adsehgal/SlugCharge/3D Housing Model/3D_Internal.jpg

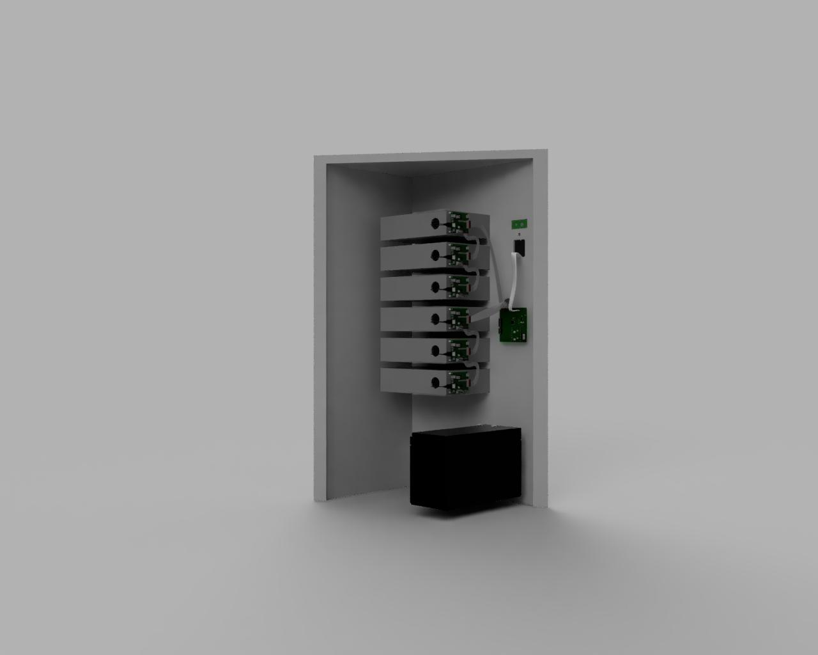
3D Housing Model/3D_Internal.jpg
