adsehgal/SlugCharge/3D Housing Model/Orthographic_Drawing_Final.pdf

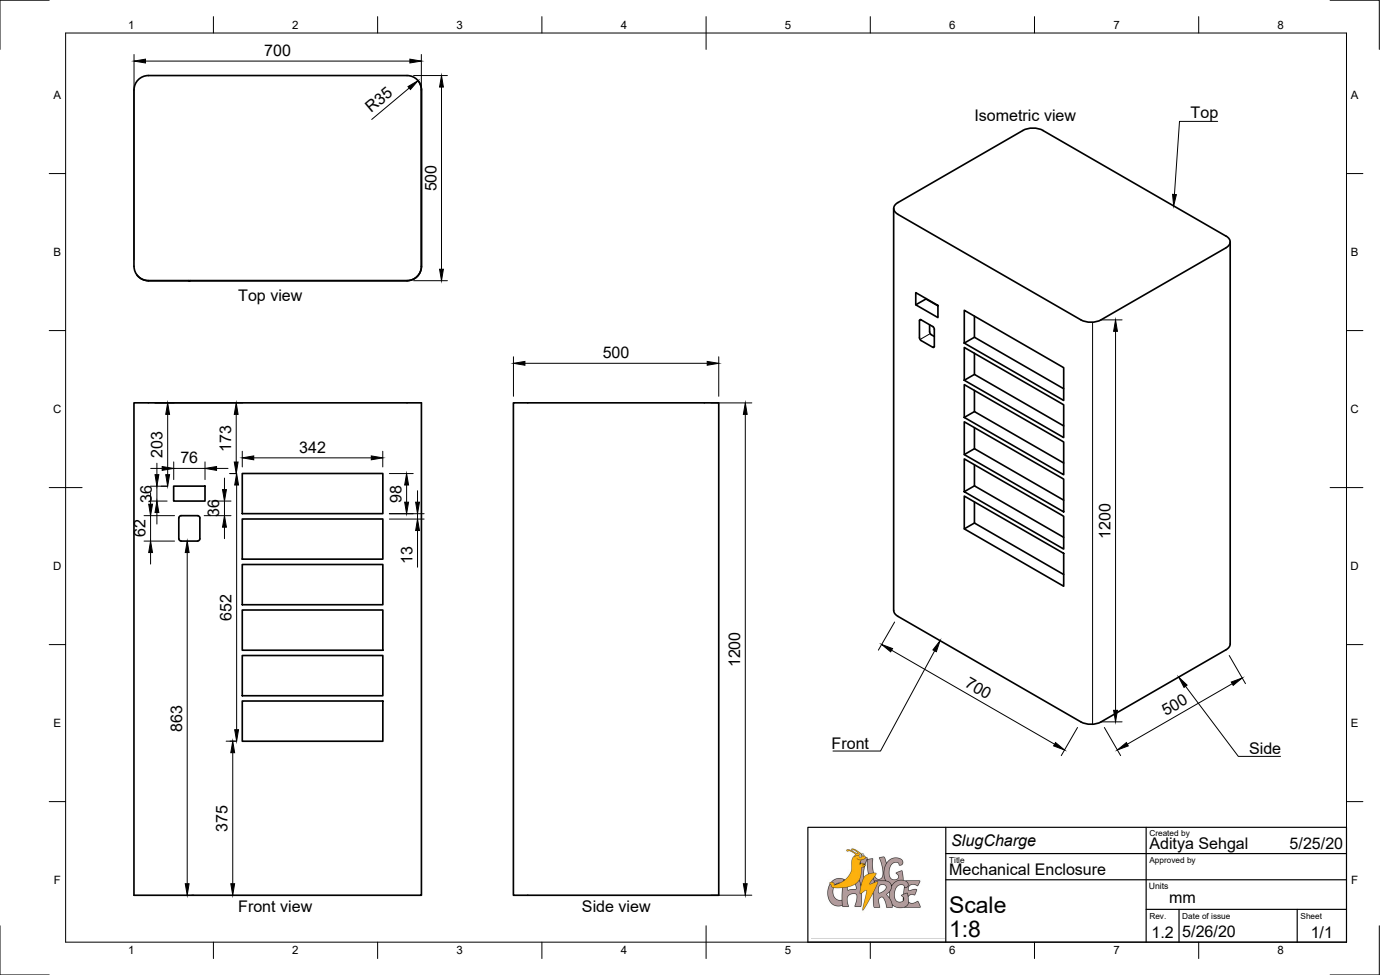
[picture p21: page 1]
Created by; SlugCharge; Aditya Sehgal; Front view; Top view; Side view; Isometric view; Front; Side; Top

Title Mechanical Enclosure | Approved by

Scale 1:8 | Units mm

Rev. 1.2 | Date of issue 5/26/20 | Sheet 1/1
