adsehgal/SlugCharge/SlugCharge_Testbench_V1.0/Schematic & Layout PDFs/Schematic.pdf

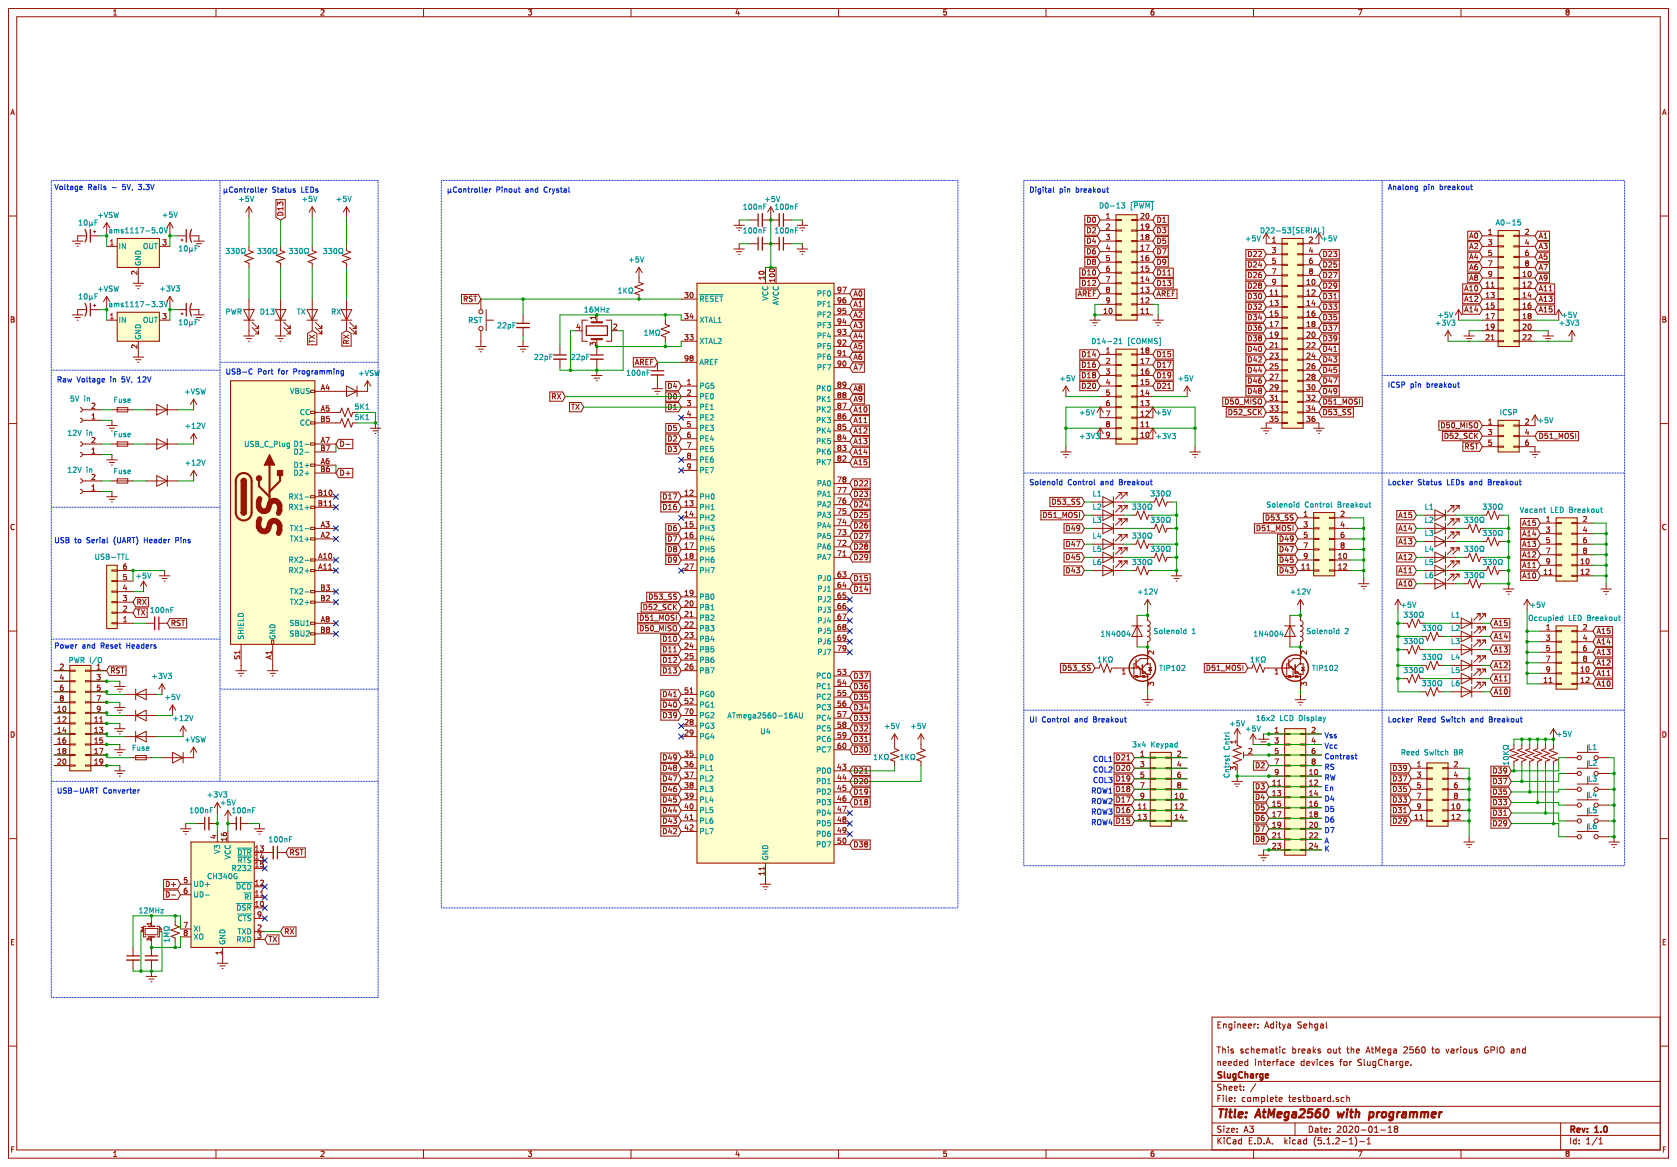
[picture p42: page 1]
