adsehgal/SlugCharge/LM2576/layout.pdf

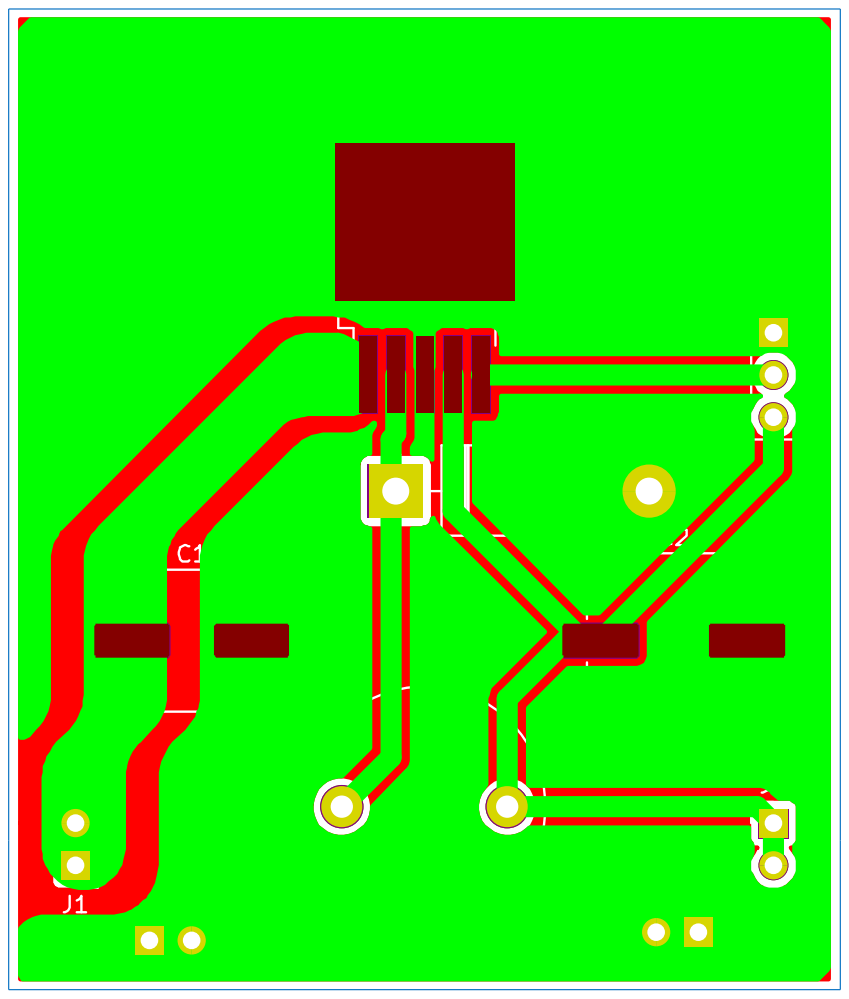
[picture p43: page 1]
